joshkuminski/OpenVision-Traffic-Camera/Build_Images/3D Model_iso.PNG

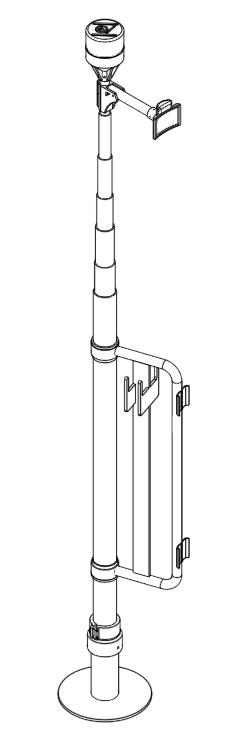
Build_Images/3D Model_iso.PNG
