joshkuminski/OpenVision-Traffic-Camera/Build_Images/3D Model_iso_control.PNG

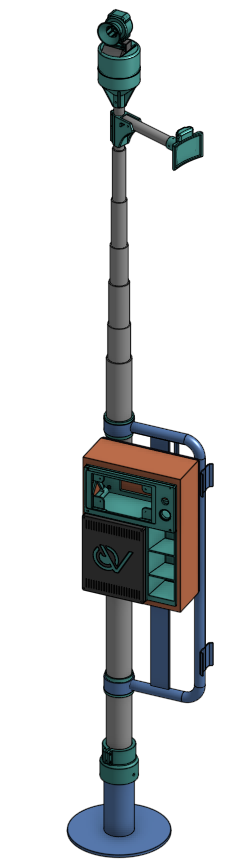
Build_Images/3D Model_iso_control.PNG
